goopypanther/uvc_hepa_air_purifier/cad/foot.FCStd

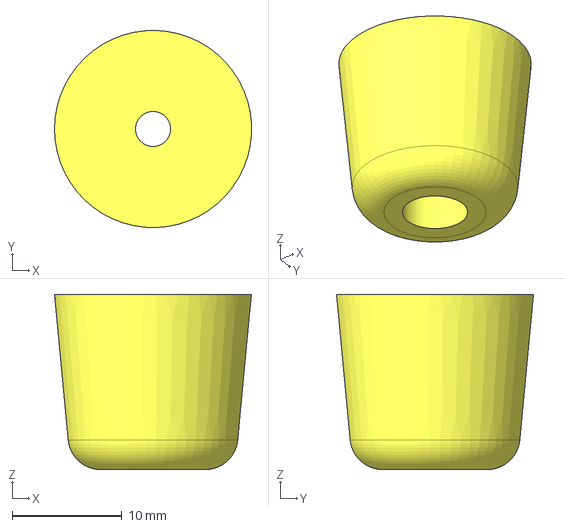
[picture p15: CAD file, 2020-08-20]
cad/foot.FCStd
18.0 x 18.0 x 16.0 mm
