goopypanther/uvc_hepa_air_purifier/cad/air_filter.FCStd

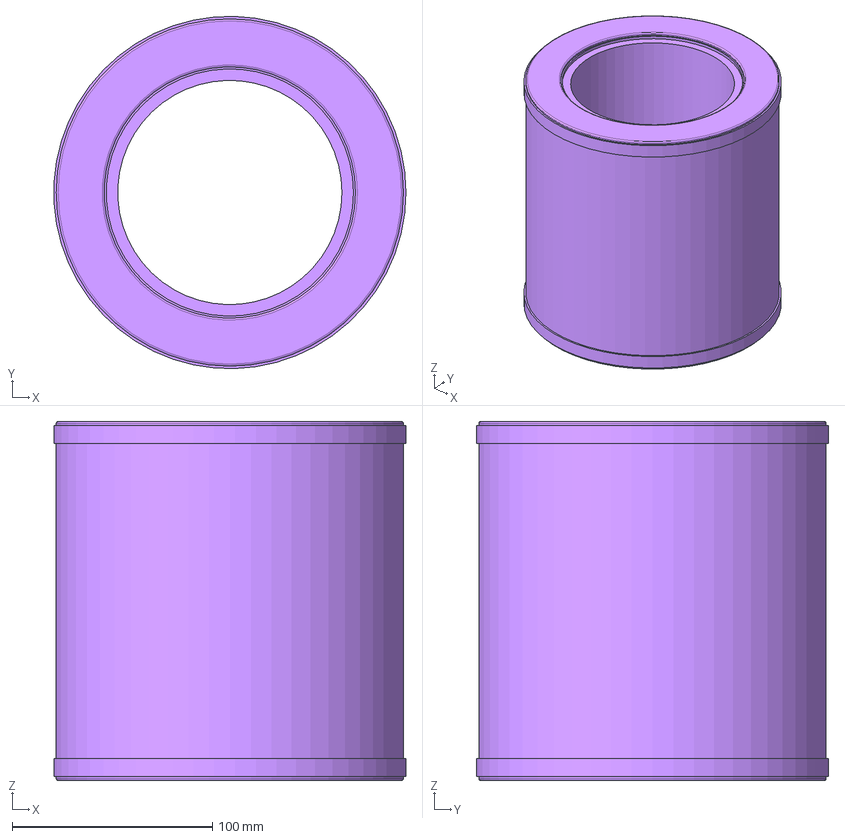
[picture p16: CAD file, 2020-08-20]
cad/air_filter.FCStd
175.8 x 175.9 x 179.5 mm
