goopypanther/uvc_hepa_air_purifier/cad/baffle_cap.FCStd

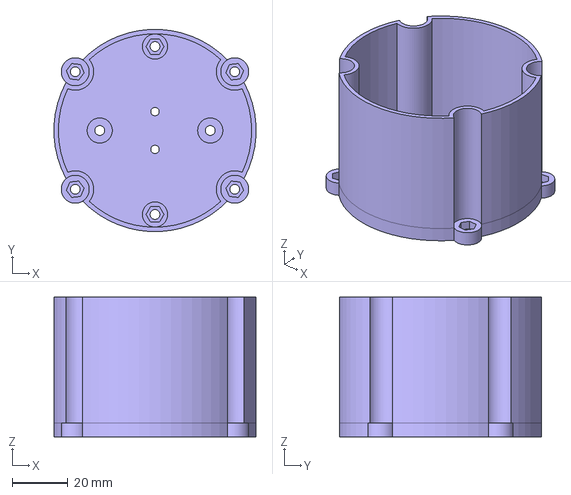
[picture p17: CAD file, 2020-08-20]
cad/baffle_cap.FCStd
72.2 x 72.2 x 50.0 mm
