goopypanther/uvc_hepa_air_purifier/cad/top_cap.FCStd

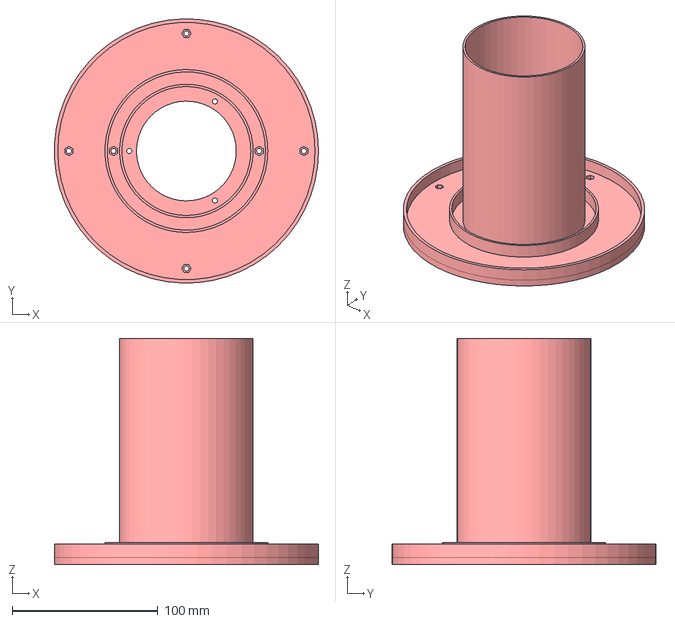
[picture p18: CAD file, 2020-08-20]
cad/top_cap.FCStd
180.9 x 180.9 x 155.0 mm
