goopypanther/uvc_hepa_air_purifier/sim/uvc_air_filter_psu.asc

C1: cap; 4.7µ
C2: cap; 5.6µ
C3: cap; 470µ
D1: diode; 1SR154-400
D2: diode; 1SR154-400
D3: diode; 1SR154-400
D4: diode; 1SR154-400
D5: zener; BZX84C12L
D6: zener; BZX84C10L
D7: schottky; BZX84C10L
R1: res; 1Meg
R3: res; 100
R4: res; 1Meg
R5: res; 1
R6: res; 2
V1: voltage; SINE(0 170 60 0 0 90)
Named nets: 0
.tran 2
